nyu-rdt/RDT26-EE/platformio_projects/RDT_2025_26_TEENSY4_1/src/drivers/motor/can_driver.cpp

#include <FlexCAN_T4.h>
#include "can_driver.h"
#include "config.h"

static_assert(CAN_ID_LEFT_MOTOR != CAN_ID_RIGHT_MOTOR,
              "CAN IDs must be unique: LEFT and RIGHT motors share an ID.");
static_assert(CAN_ID_LEFT_MOTOR != CAN_ID_EXCAVATION_MOTOR,
              "CAN IDs must be unique: LEFT and EXCAVATION motors share an ID.");
static_assert(CAN_ID_RIGHT_MOTOR != CAN_ID_EXCAVATION_MOTOR,
              "CAN IDs must be unique: RIGHT and EXCAVATION motors share an ID.");

static FlexCAN_T4<CAN1, RX_SIZE_256, TX_SIZE_16> can1;

void CAN_Init() {
    can1.begin();
    can1.setBaudRate(CAN_BAUD_RATE);
}

void CAN_SendMotorSpeed(uint32_t canId, float speed) {
    CAN_message_t msg;
    msg.flags.extended = 1;
    msg.id = canId;
    msg.len = 4;
    
    int32_t value = (int32_t)(speed * 100000.0f);
    msg.buf[0] = (value >> 24) & 0xFF;
    msg.buf[1] = (value >> 16) & 0xFF;
    msg.buf[2] = (value >> 8) & 0xFF;
    msg.buf[3] = value & 0xFF;
    
    can1.write(msg);
}

/*
// Alternate test function for standard 11-bit frame format.
// Keep commented for now; you can swap calls to this version for A/B testing.
void CAN_SendMotorSpeed(uint32_t canId, float speed) {
    CAN_message_t msg;
    msg.flags.extended = 0;
    msg.id = canId;
    msg.len = 4;

    int32_t value = (int32_t)(speed * 100000.0f);
    msg.buf[0] = (value >> 24) & 0xFF;
    msg.buf[1] = (value >> 16) & 0xFF;
    msg.buf[2] = (value >> 8) & 0xFF;
    msg.buf[3] = value & 0xFF;

    can1.write(msg);
}
*/

void CAN_SendLocomotion(float left, float right) {
    CAN_SendMotorSpeed(CAN_ID_LEFT_MOTOR, -left);
    CAN_SendMotorSpeed(CAN_ID_RIGHT_MOTOR, right);
}

void CAN_SendExcavation(float speed) {
    CAN_SendMotorSpeed(CAN_ID_EXCAVATION_MOTOR, speed);
}
